clubroboticagranada/MASAYLO-CRG/docs/Miscelanea/lic.md

# <FONT COLOR=#8B008B>Licencias</font>

***

* [Licencia MIT](https://es.wikipedia.org/wiki/Licencia_MIT) incluida en la creación del repositorio.

* Creative Commons Atribución-CompartirIgual 4.0 International ("CC BY-SA"). [CC BY-SA 4.0](https://creativecommons.org/licenses/by-sa/4.0/deed.es)  

<center>

Imagen de la licencia  

</center>

* Open Source Hardware (OSHW). [Enlace a la versión V 1.0 original de la licencia](https://freedomdefined.org/OSHW) - [Enlace a la traducción de la versión V 1.0 original de la licencia](https://freedomdefined.org/OSHW/translations/es) - [Spanish - Open Source Hardware Association](https://www.oshwa.org/definition/spanish/)

<center>

logo OSHW

</center>
