clubroboticagranada/MASAYLO-CRG/docs/img/3D/imagenes/capturas/01-base.png

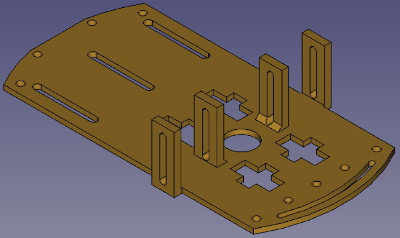
docs/img/3D/imagenes/capturas/01-base.png
