clubroboticagranada/MASAYLO-CRG/docs/img/3D/imagenes/capturas/04-soporte-zumbador.png

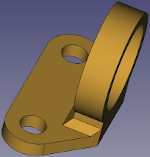
docs/img/3D/imagenes/capturas/04-soporte-zumbador.png
