clubroboticagranada/MASAYLO-CRG/docs/img/3D/imagenes/capturas/06a-ballcaster.png

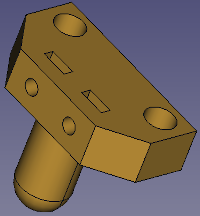
docs/img/3D/imagenes/capturas/06a-ballcaster.png
