clubroboticagranada/MASAYLO-CRG/docs/img/3D/imagenes/capturas/06b-porta-sensores-IR.png

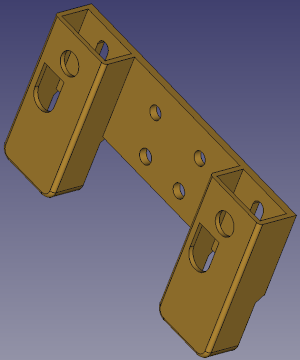
docs/img/3D/imagenes/capturas/06b-porta-sensores-IR.png
