clubroboticagranada/MASAYLO-CRG/docs/img/3D/imagenes/capturas/07a-ruedas.png

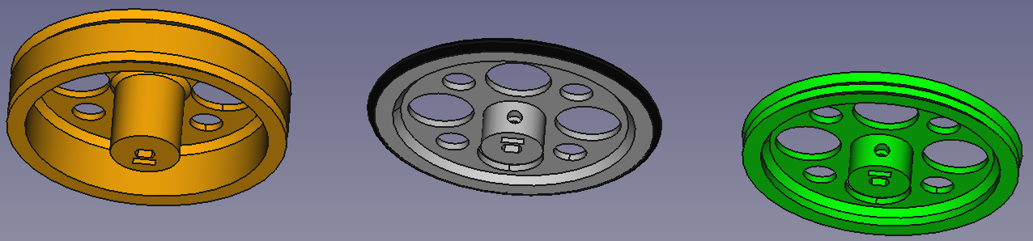
docs/img/3D/imagenes/capturas/07a-ruedas.png
