clubroboticagranada/MASAYLO-CRG/docs/img/3D/imagenes/capturas/08a-soporte-servo.png

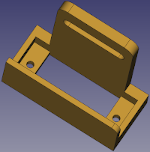
docs/img/3D/imagenes/capturas/08a-soporte-servo.png
