clubroboticagranada/MASAYLO-CRG/docs/img/3D/imagenes/capturas/08b-soporte-ultras-pala-servo.png

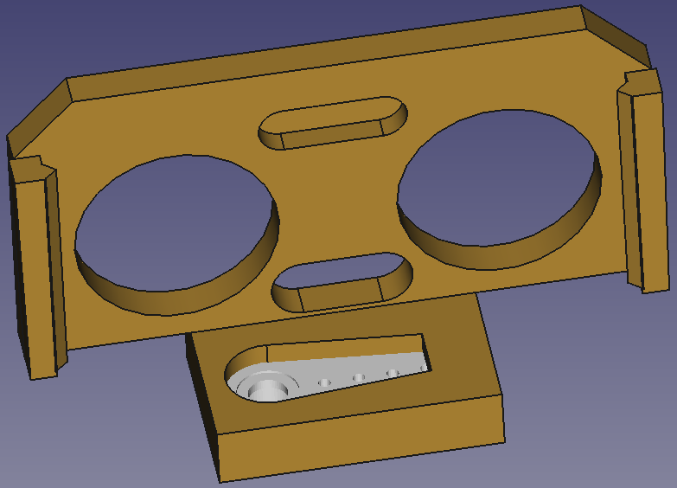
docs/img/3D/imagenes/capturas/08b-soporte-ultras-pala-servo.png
