clubroboticagranada/MASAYLO-CRG/docs/img/3D/imagenes/capturas/10-plataforma-superior.png

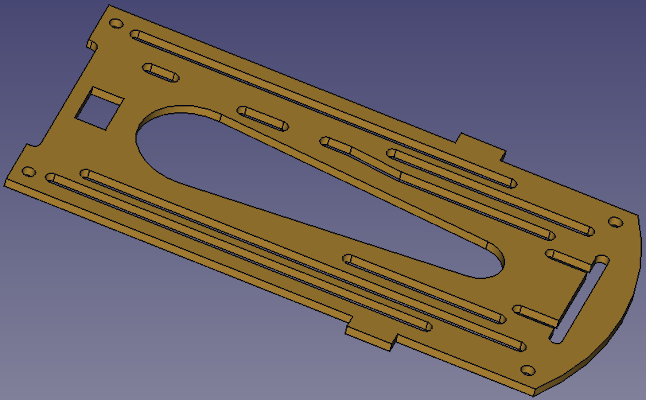
docs/img/3D/imagenes/capturas/10-plataforma-superior.png
