clubroboticagranada/MASAYLO-CRG/docs/img/3D/imagenes/capturas/11b-brazo.png

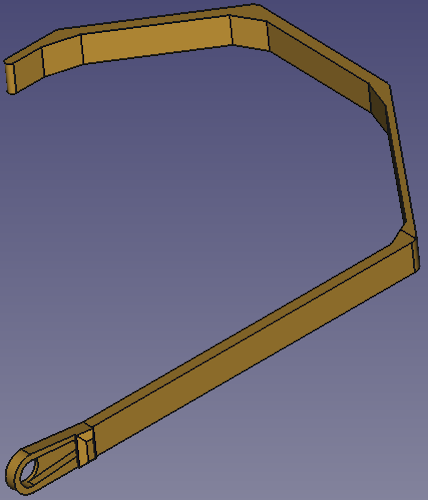
docs/img/3D/imagenes/capturas/11b-brazo.png
