clubroboticagranada/MASAYLO-CRG/docs/img/3D/imagenes/capturas/16a-opcion-ultrasonidos-fijo.png

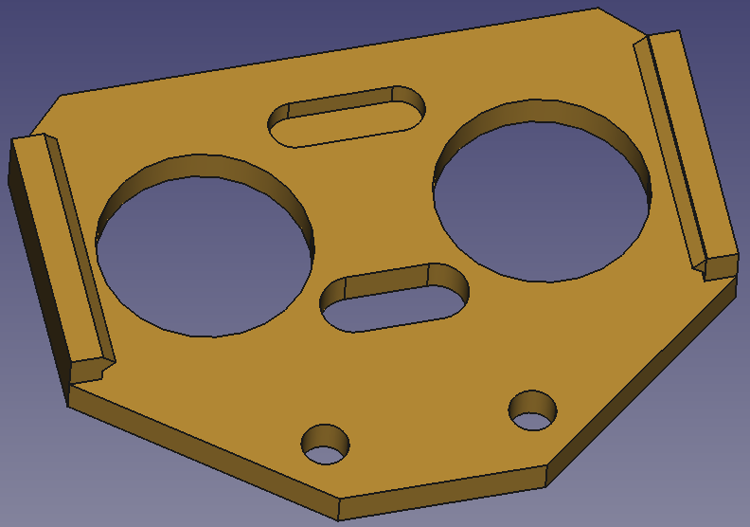
docs/img/3D/imagenes/capturas/16a-opcion-ultrasonidos-fijo.png
