clubroboticagranada/MASAYLO-CRG/docs/img/3D/imagenes/capturas/16b-soporte.png

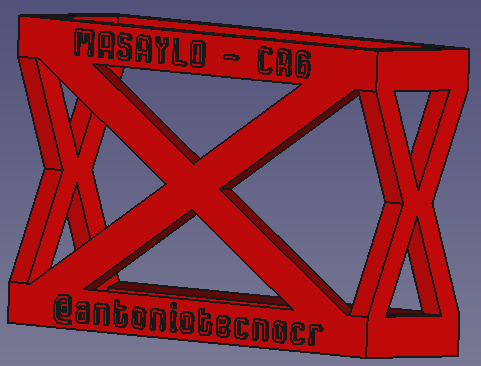
docs/img/3D/imagenes/capturas/16b-soporte.png
