clubroboticagranada/MASAYLO-CRG/docs/img/3D/imagenes/capturas/111a-separador-M3x5.png

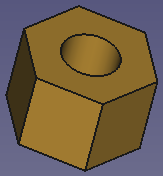
docs/img/3D/imagenes/capturas/111a-separador-M3x5.png
