clubroboticagranada/MASAYLO-CRG/docs/img/3D/imagenes/capturas/disco-encoder.png

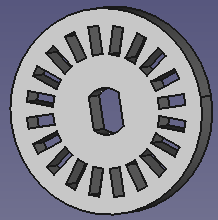
docs/img/3D/imagenes/capturas/disco-encoder.png
