clubroboticagranada/MASAYLO-CRG/docs/img/3D/imagenes/capturas/separador-M3x28.png

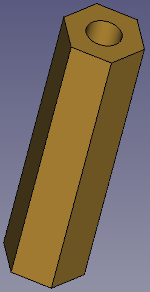
docs/img/3D/imagenes/capturas/separador-M3x28.png
