clubroboticagranada/MASAYLO-CRG/docs/img/3D/imagenes/fotos/01-base.jpeg

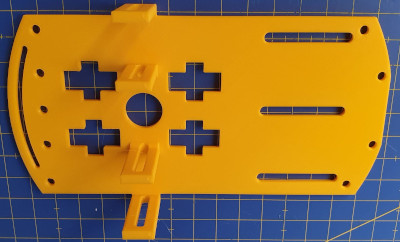
docs/img/3D/imagenes/fotos/01-base.jpeg
