clubroboticagranada/MASAYLO-CRG/docs/img/3D/imagenes/fotos/04-soporte-zumbador.jpeg

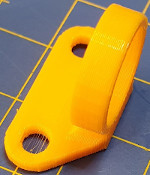
docs/img/3D/imagenes/fotos/04-soporte-zumbador.jpeg
