clubroboticagranada/MASAYLO-CRG/docs/img/3D/imagenes/fotos/06a-ballcaster.jpeg

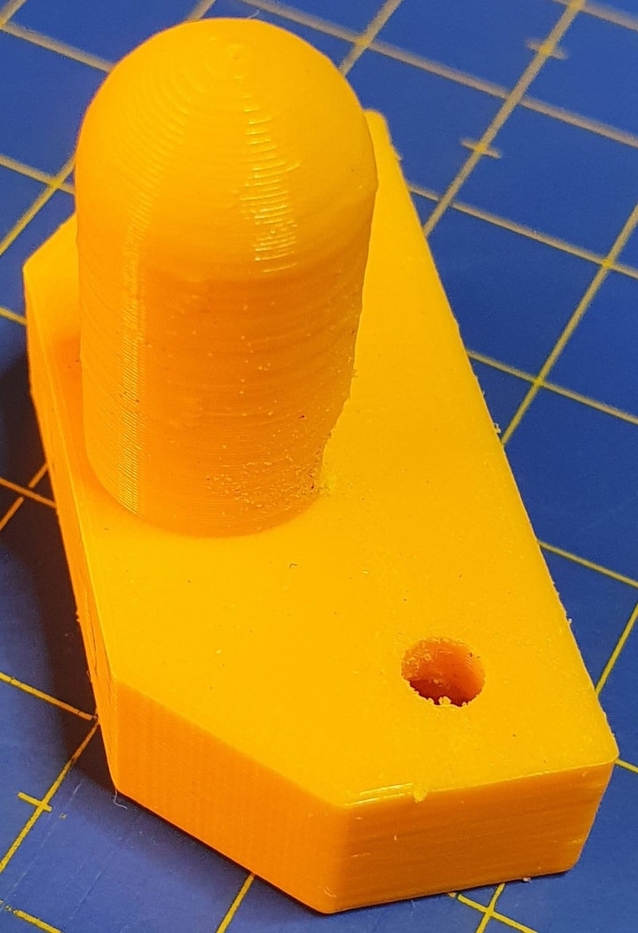
docs/img/3D/imagenes/fotos/06a-ballcaster.jpeg
