clubroboticagranada/MASAYLO-CRG/docs/img/3D/imagenes/fotos/06b-porta-sensores-IR.jpeg

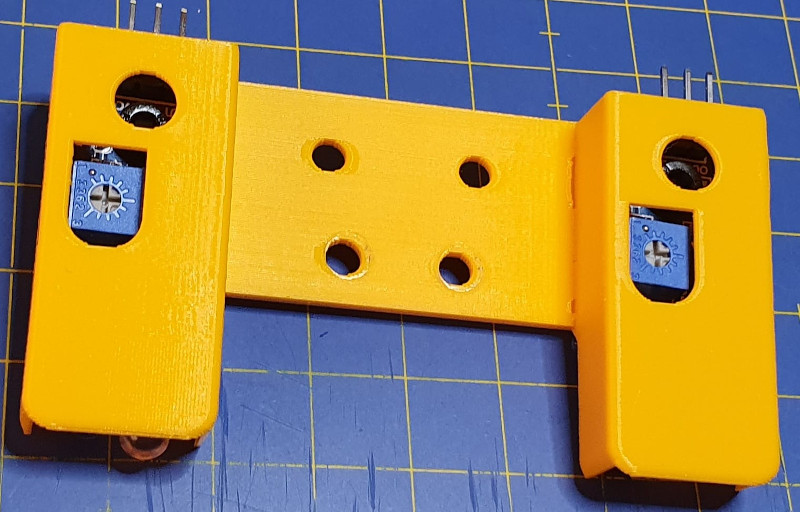
docs/img/3D/imagenes/fotos/06b-porta-sensores-IR.jpeg
