clubroboticagranada/MASAYLO-CRG/docs/img/3D/imagenes/fotos/07a-ruedas-una-junta.jpeg

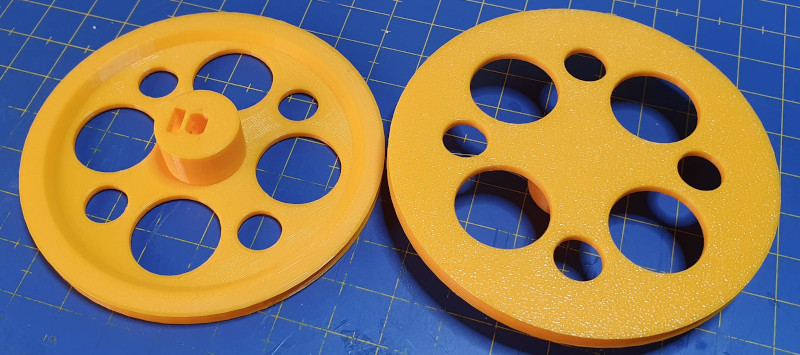
docs/img/3D/imagenes/fotos/07a-ruedas-una-junta.jpeg
