clubroboticagranada/MASAYLO-CRG/docs/img/3D/imagenes/fotos/08a-soporte-servo.jpeg

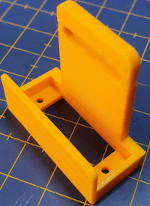
docs/img/3D/imagenes/fotos/08a-soporte-servo.jpeg
