clubroboticagranada/MASAYLO-CRG/docs/img/3D/imagenes/fotos/08b-soporte-ultras-pala-servo.jpeg

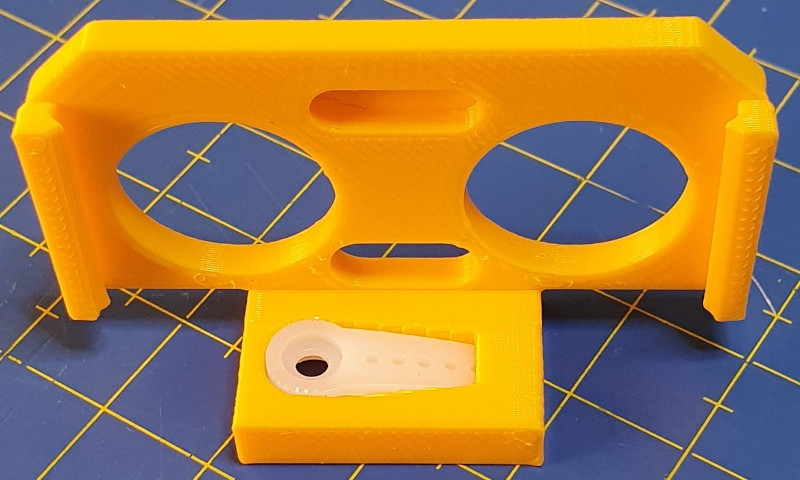
docs/img/3D/imagenes/fotos/08b-soporte-ultras-pala-servo.jpeg
