clubroboticagranada/MASAYLO-CRG/docs/img/3D/imagenes/fotos/10-plataforma-superior.jpeg

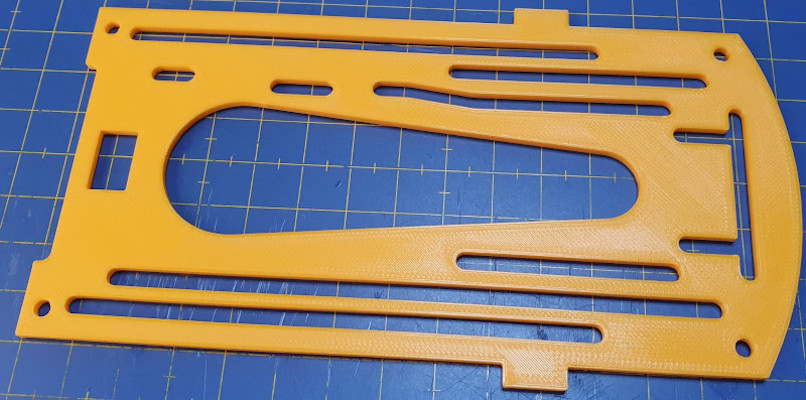
docs/img/3D/imagenes/fotos/10-plataforma-superior.jpeg
