clubroboticagranada/MASAYLO-CRG/docs/img/3D/imagenes/fotos/11b-brazo.jpeg

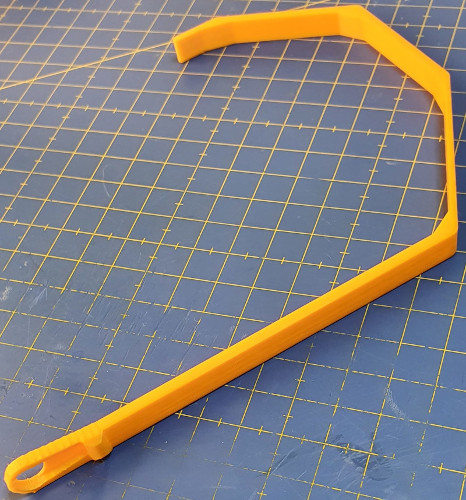
docs/img/3D/imagenes/fotos/11b-brazo.jpeg
