clubroboticagranada/MASAYLO-CRG/docs/img/3D/imagenes/fotos/16a-opcion-ultrasonidos-fijo.jpeg

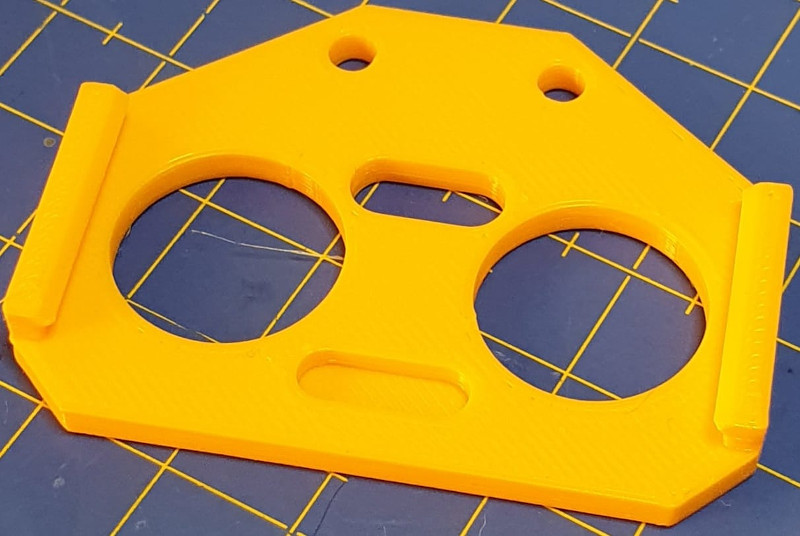
docs/img/3D/imagenes/fotos/16a-opcion-ultrasonidos-fijo.jpeg
