clubroboticagranada/MASAYLO-CRG/docs/img/3D/imagenes/fotos/reformados/ballcaster-con-tornillo.png

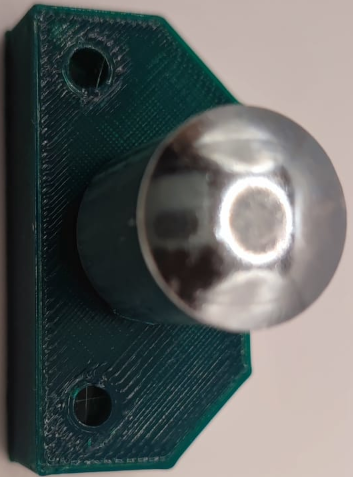
docs/img/3D/imagenes/fotos/reformados/ballcaster-con-tornillo.png
