clubroboticagranada/MASAYLO-CRG/docs/img/3D/imagenes/fotos/reformados/ballcaster-impresa.png

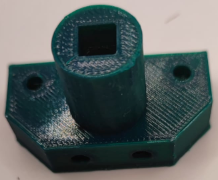
docs/img/3D/imagenes/fotos/reformados/ballcaster-impresa.png
