clubroboticagranada/MASAYLO-CRG/docs/img/3D/imagenes/fotos/reformados/detalle-refuerzo-brazo.png

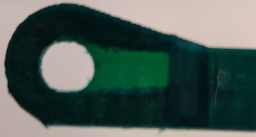
docs/img/3D/imagenes/fotos/reformados/detalle-refuerzo-brazo.png
