clubroboticagranada/MASAYLO-CRG/docs/img/3D/modificados/imagenes/fotos/tornillo-tuerca-M6x30.png

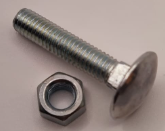
docs/img/3D/modificados/imagenes/fotos/tornillo-tuerca-M6x30.png
