clubroboticagranada/MASAYLO-CRG/docs/img/masayloBlockly/instala1.jpg

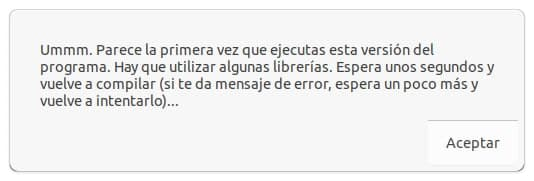
docs/img/masayloBlockly/instala1.jpg
