clubroboticagranada/MASAYLO-CRG/docs/img/masayloBlockly/instala2.jpg

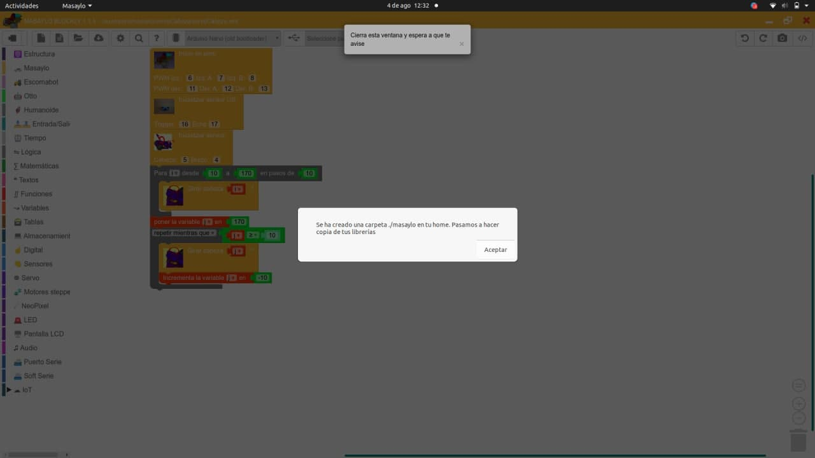
docs/img/masayloBlockly/instala2.jpg
