clubroboticagranada/MASAYLO-CRG/docs/img/masayloBlockly/instala3.jpg

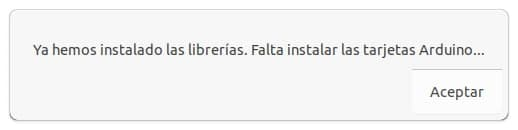
docs/img/masayloBlockly/instala3.jpg
