clubroboticagranada/MASAYLO-CRG/docs/img/masayloBlockly/instala4.jpg

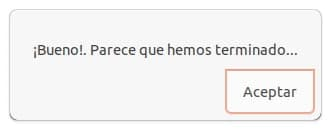
docs/img/masayloBlockly/instala4.jpg
