clubroboticagranada/MASAYLO-CRG/docs/img/masayloBlockly/instala5.jpg

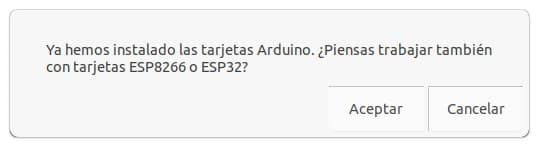
docs/img/masayloBlockly/instala5.jpg
