clubroboticagranada/MASAYLO-CRG/docs/img/masayloBlockly/instala6.jpg

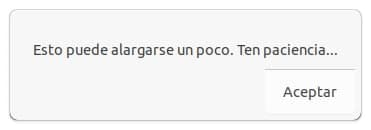
docs/img/masayloBlockly/instala6.jpg
