clubroboticagranada/MASAYLO-CRG/docs/img/masayloBlockly/instala7.jpg

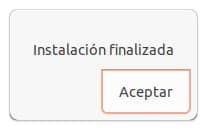
docs/img/masayloBlockly/instala7.jpg
