clubroboticagranada/MASAYLO-CRG/docs/img/masayloBlockly/organizacionGeneral.png

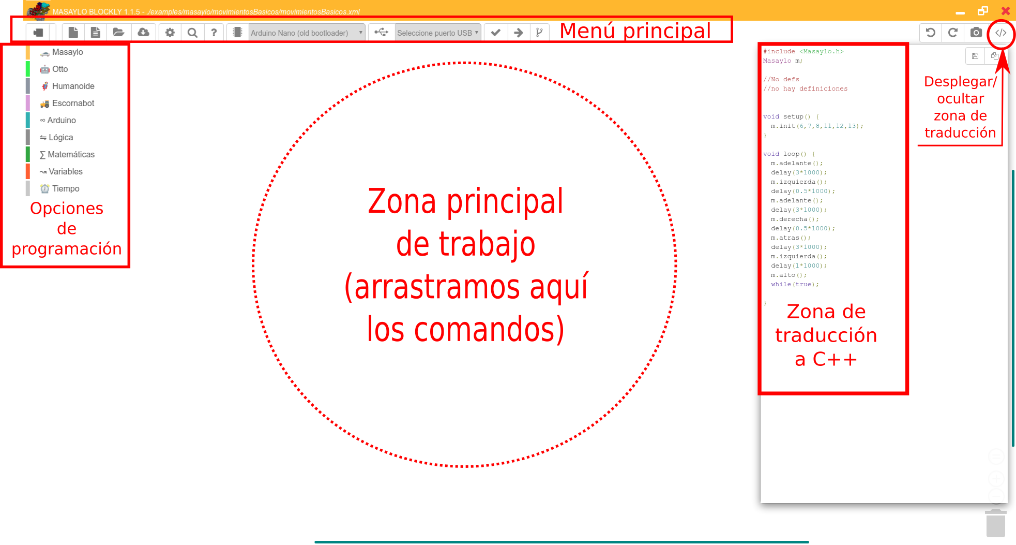
docs/img/masayloBlockly/organizacionGeneral.png
