clubroboticagranada/MASAYLO-CRG/docs/img/masayloBlockly/primeraPantalla.png

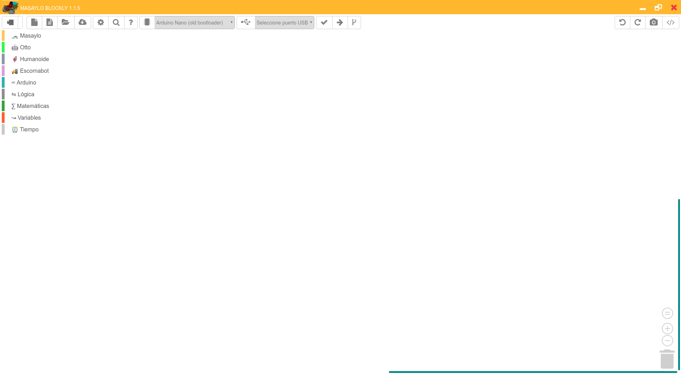
docs/img/masayloBlockly/primeraPantalla.png
