clubroboticagranada/MASAYLO-CRG/docs/img/merchandising/pegatina-rectangular/qr.png

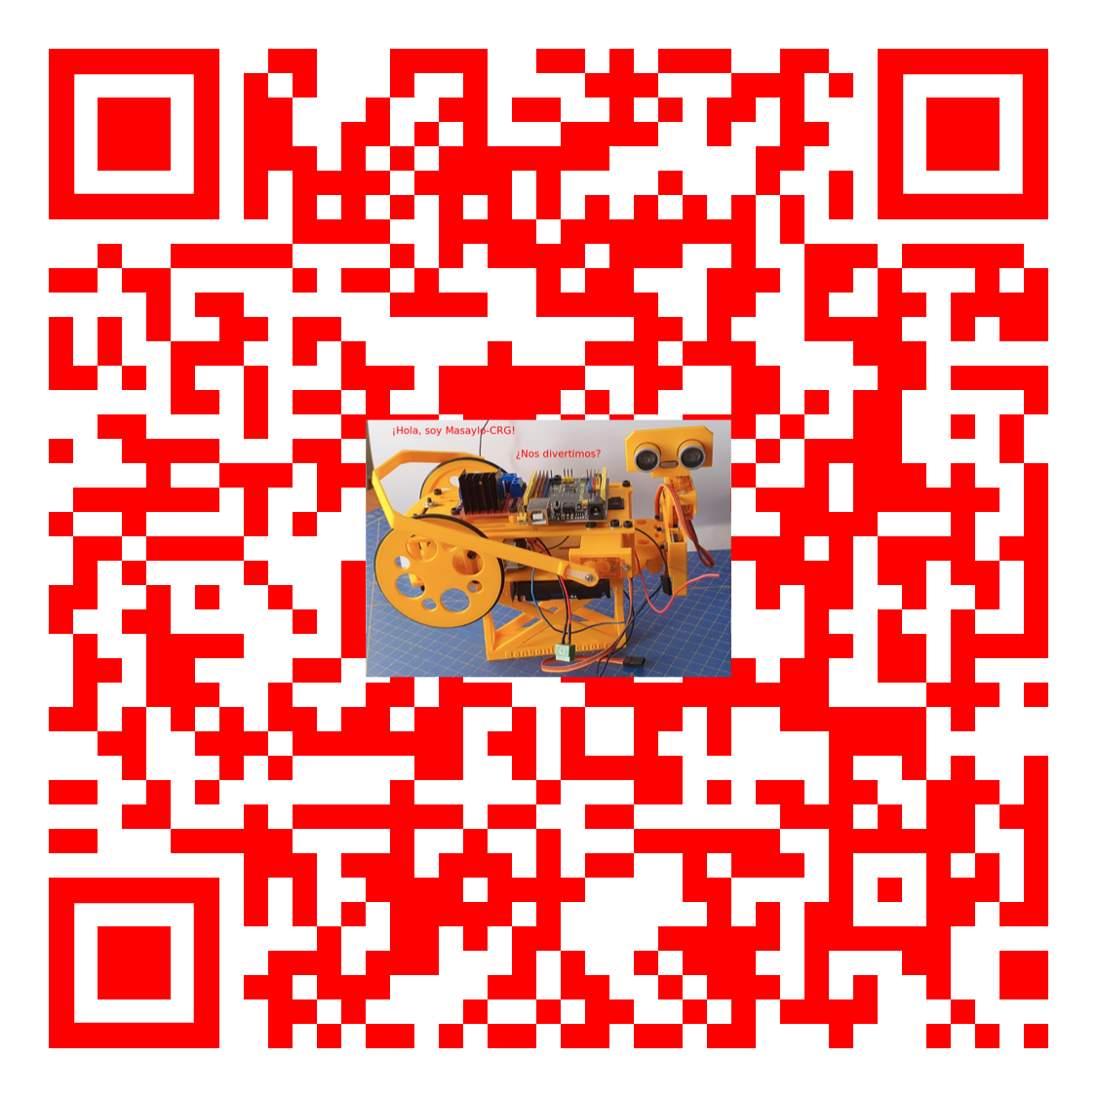
docs/img/merchandising/pegatina-rectangular/qr.png
