clubroboticagranada/MASAYLO-CRG/docs/img/3D/step/base-servo.step

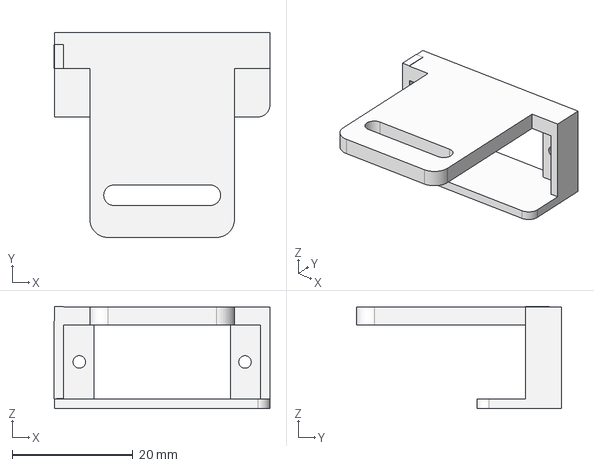
[picture p127: CAD file, 2021-06-13]
docs/img/3D/step/base-servo.step
35.8 x 34.0 x 16.9 mm
