clubroboticagranada/MASAYLO-CRG/docs/img/3D/src/base-servo-src.FCStd

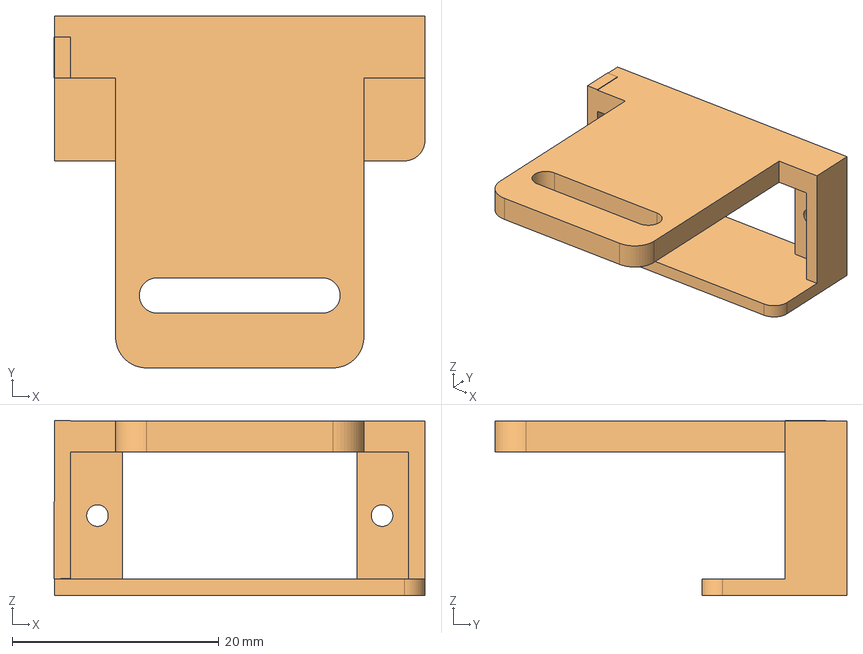
[picture p128: CAD file, 2021-06-13]
docs/img/3D/src/base-servo-src.FCStd
35.8 x 34.0 x 16.9 mm
base-servo-copy
