clubroboticagranada/MASAYLO-CRG/docs/img/3D/src/disco-encoder.FCStd

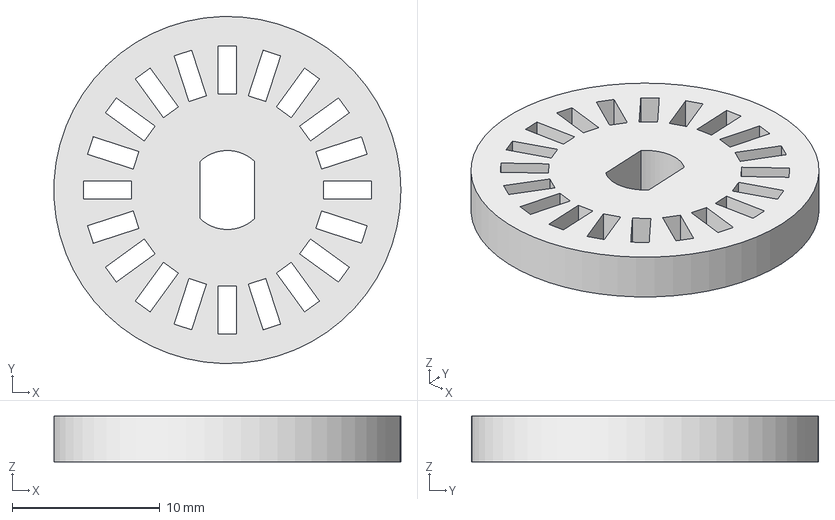
[picture p129: CAD file, 2021-06-13]
docs/img/3D/src/disco-encoder.FCStd
23.5 x 23.5 x 3.10 mm
