clubroboticagranada/MASAYLO-CRG/docs/img/3D/step/soporte-zumbador.step

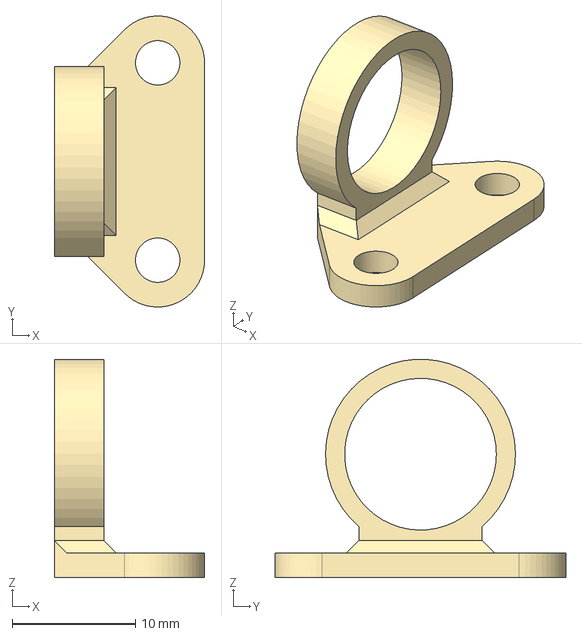
[picture p130: CAD file, 2021-06-13]
docs/img/3D/step/soporte-zumbador.step
12.2 x 23.6 x 17.7 mm
