clubroboticagranada/MASAYLO-CRG/docs/img/3D/src/brazo-src.FCStd

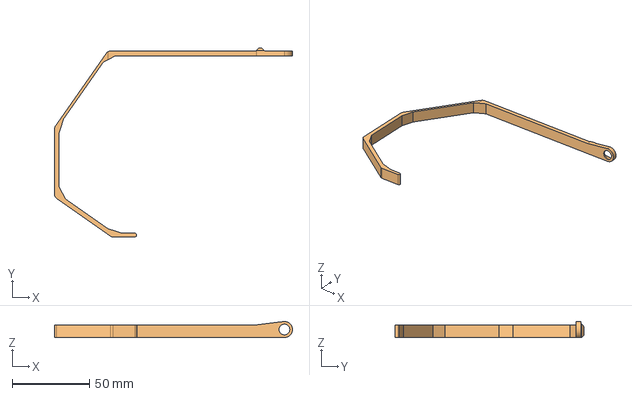
[picture p131: CAD file, 2021-06-13]
docs/img/3D/src/brazo-src.FCStd
153.6 x 122.0 x 10.4 mm
brazo-copy
