clubroboticagranada/MASAYLO-CRG/docs/img/3D/step/brazo.step

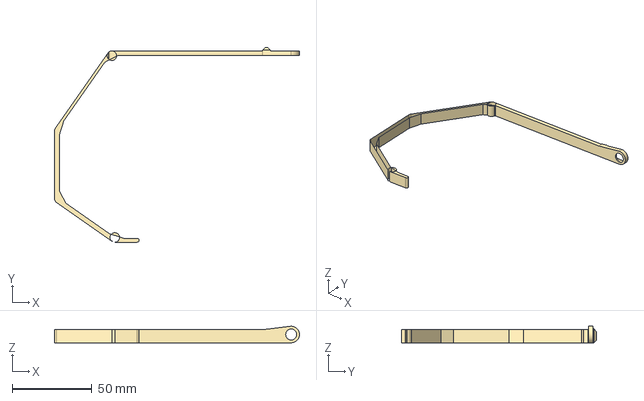
[picture p132: CAD file, 2021-06-13]
docs/img/3D/step/brazo.step
153.6 x 122.0 x 10.4 mm
