clubroboticagranada/MASAYLO-CRG/docs/img/3D/src/soporte-sensores-IR-ballcaster.FCStd

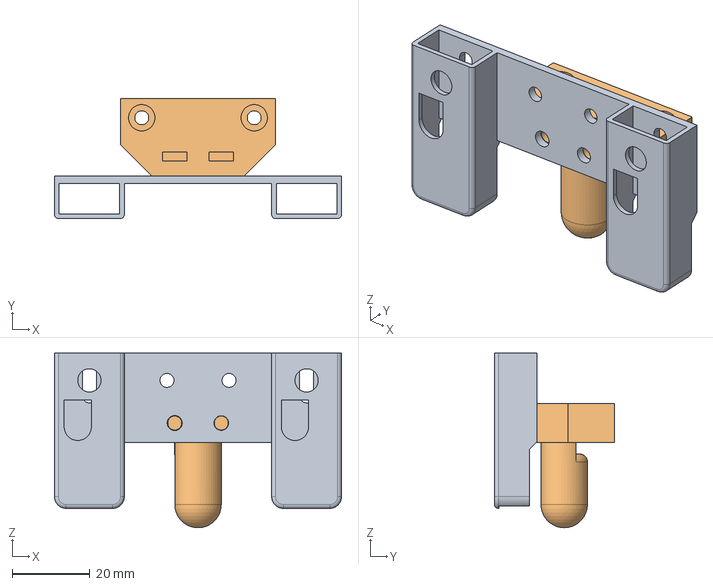
[picture p133: CAD file, 2021-06-13]
docs/img/3D/src/soporte-sensores-IR-ballcaster.FCStd
74.0 x 31.0 x 45.0 mm
porta-sensores-IR-src
ballcaster-src
