clubroboticagranada/MASAYLO-CRG/docs/img/3D/step/plataforma-superior.step

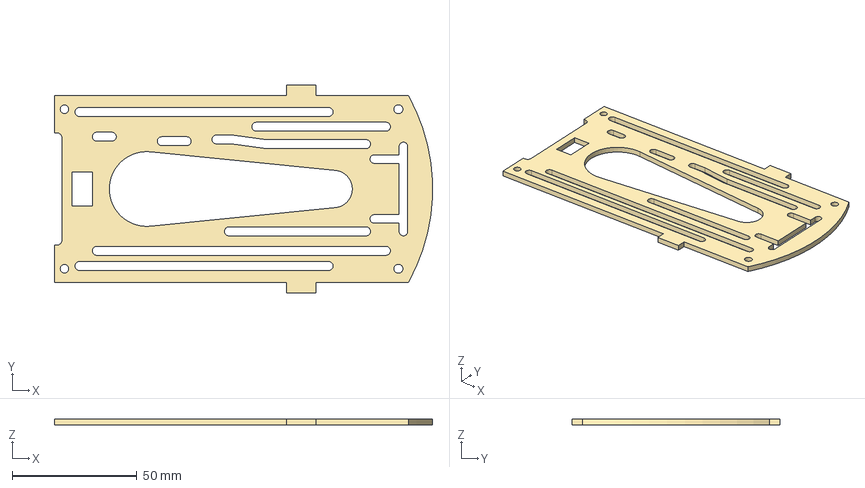
[picture p134: CAD file, 2021-06-13]
docs/img/3D/step/plataforma-superior.step
151.7 x 83.4 x 2.50 mm
