clubroboticagranada/MASAYLO-CRG/docs/img/3D/src/plataforma-base-src.FCStd

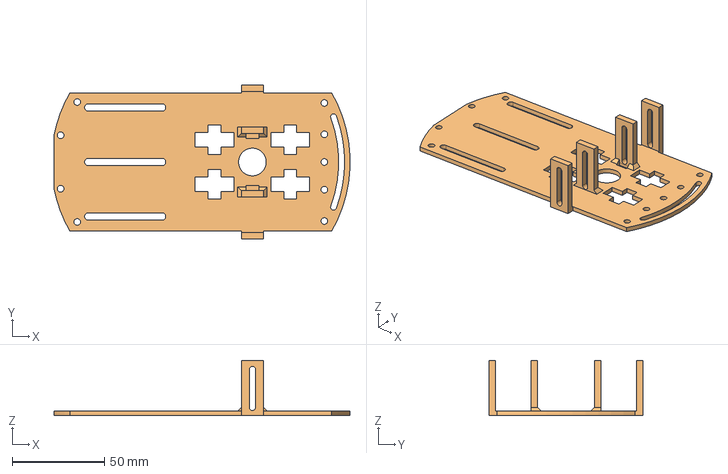
[picture p135: CAD file, 2021-06-13]
docs/img/3D/src/plataforma-base-src.FCStd
160.5 x 83.4 x 30.0 mm
plataforma-base-copy
