clubroboticagranada/MASAYLO-CRG/docs/img/3D/step/separador-M3x28.step

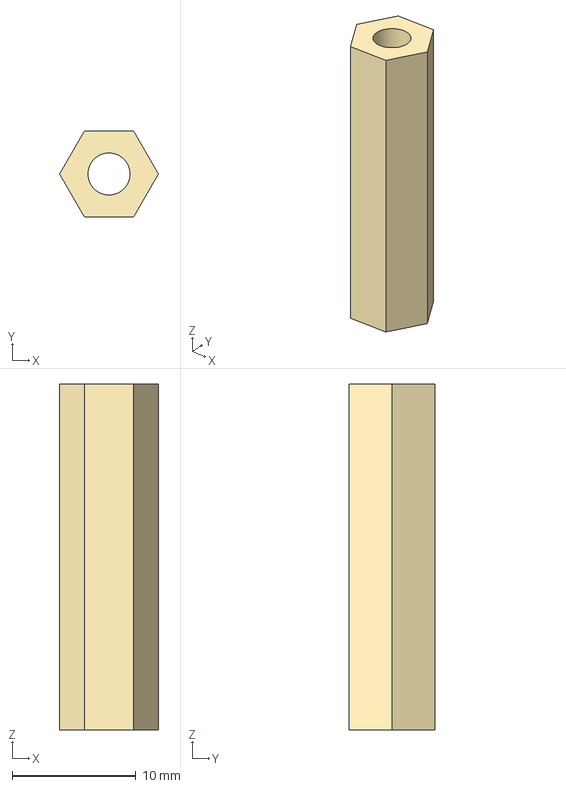
[picture p136: CAD file, 2021-06-13]
docs/img/3D/step/separador-M3x28.step
8.00 x 6.93 x 28.0 mm
