clubroboticagranada/MASAYLO-CRG/docs/img/3D/step/plataforma-base.step

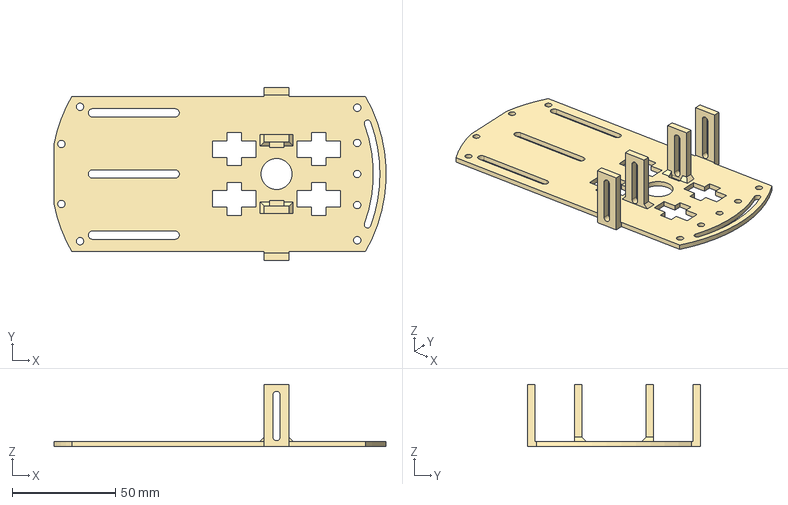
[picture p137: CAD file, 2021-06-13]
docs/img/3D/step/plataforma-base.step
160.5 x 83.4 x 30.0 mm
