clubroboticagranada/MASAYLO-CRG/docs/img/3D/step/porta-sensores-IR.step

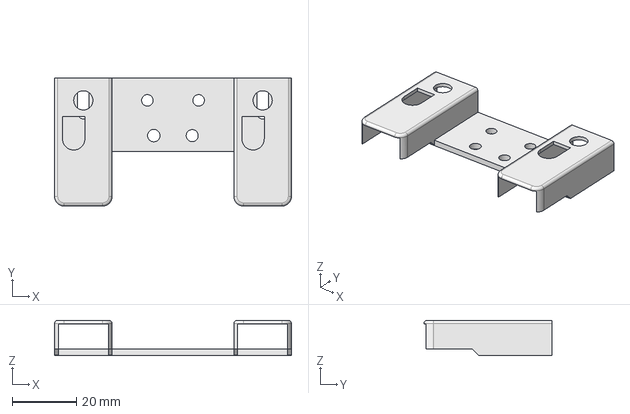
[picture p138: CAD file, 2021-06-13]
docs/img/3D/step/porta-sensores-IR.step
74.0 x 40.0 x 11.0 mm
