clubroboticagranada/MASAYLO-CRG/docs/img/3D/step/rueda-dos-juntas-ancha.step

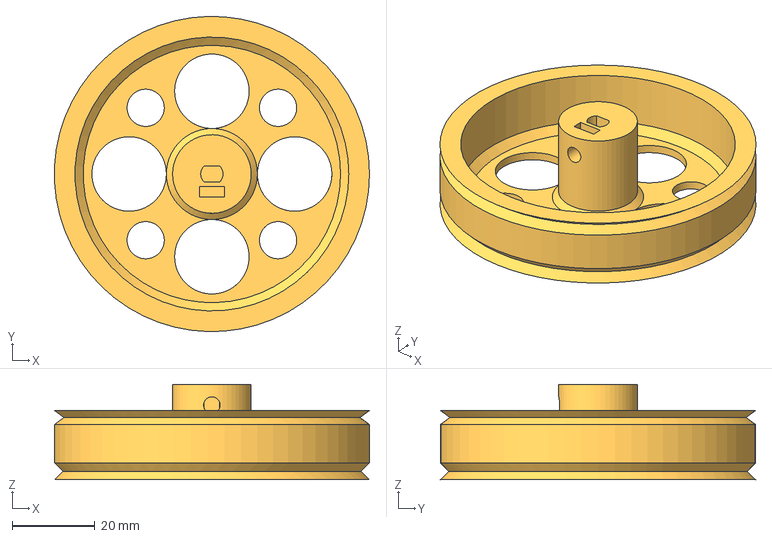
[picture p139: CAD file, 2021-06-13]
docs/img/3D/step/rueda-dos-juntas-ancha.step
76.1 x 76.2 x 23.0 mm
