clubroboticagranada/MASAYLO-CRG/docs/img/conexionado-pruebas/UNO/Driver-motor-DC-puenteH-L298.png

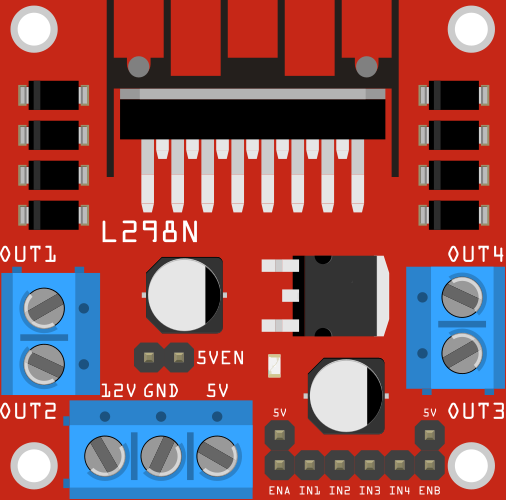
docs/img/conexionado-pruebas/UNO/Driver-motor-DC-puenteH-L298.png
