clubroboticagranada/MASAYLO-CRG/docs/img/conexionado-pruebas/UNO/Placa-Keyestudio-UNO-Ks0172.png

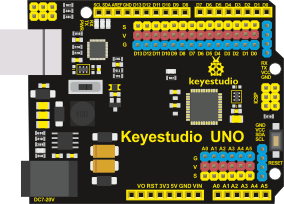
docs/img/conexionado-pruebas/UNO/Placa-Keyestudio-UNO-Ks0172.png
